Gabse/DMX2SGM/Documentation/20190912_201713.jpg

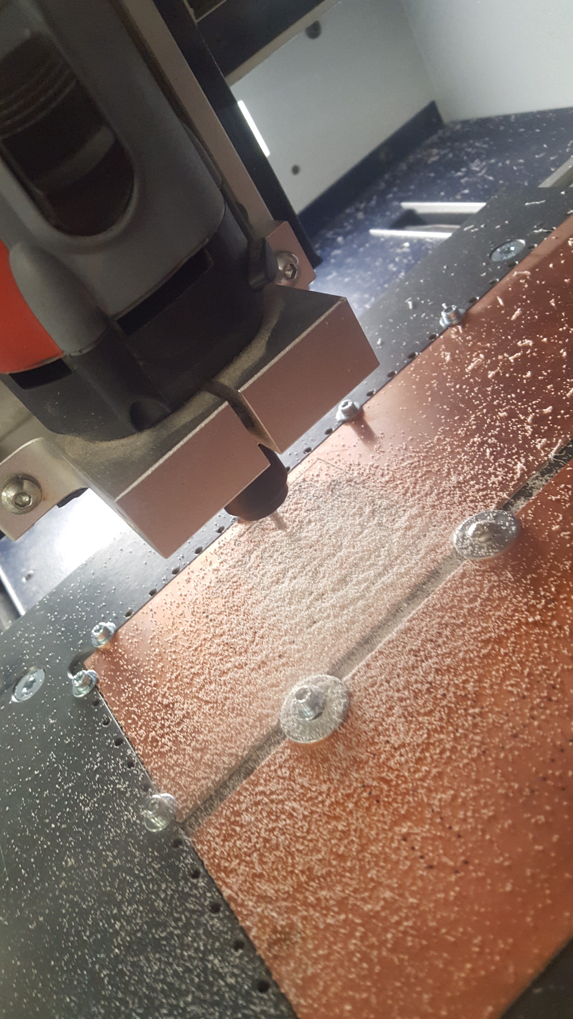
Documentation/20190912_201713.jpg
