Gabse/DMX2SGM/Documentation/20190912_203418.jpg

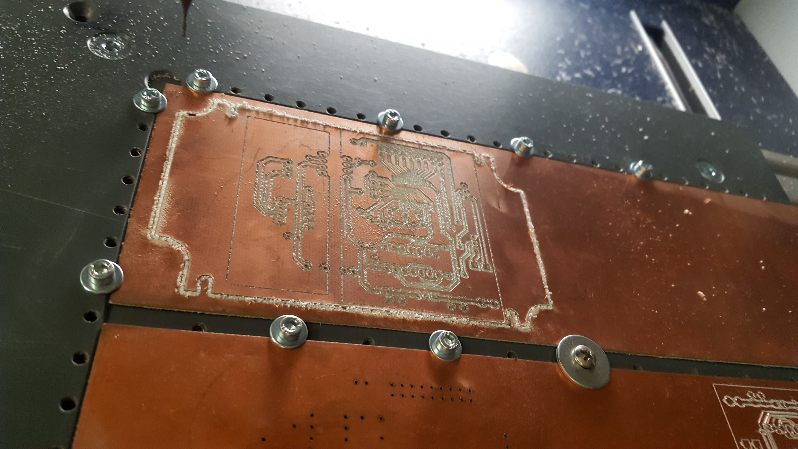
Documentation/20190912_203418.jpg
