Gabse/DMX2SGM/Documentation/20190913_112044.jpg

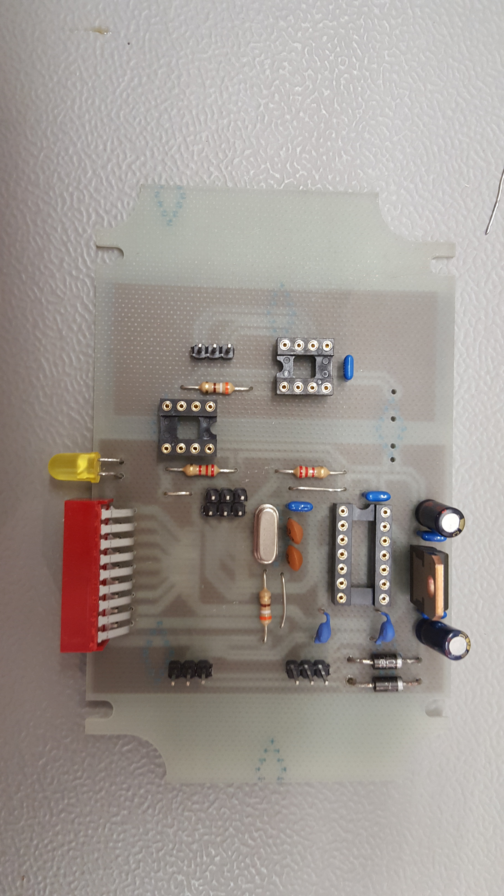
Documentation/20190913_112044.jpg
