Gabse/DMX2SGM/Documentation/20191015_202654.jpg

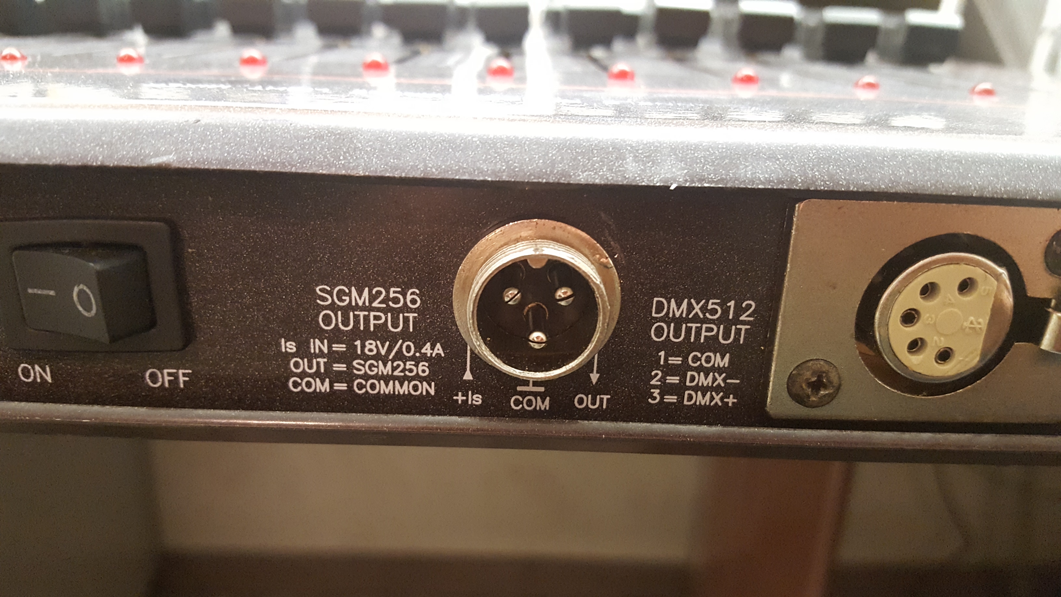
Documentation/20191015_202654.jpg
