Gabse/DMX2SGM/Documentation/20191113_215739.jpg

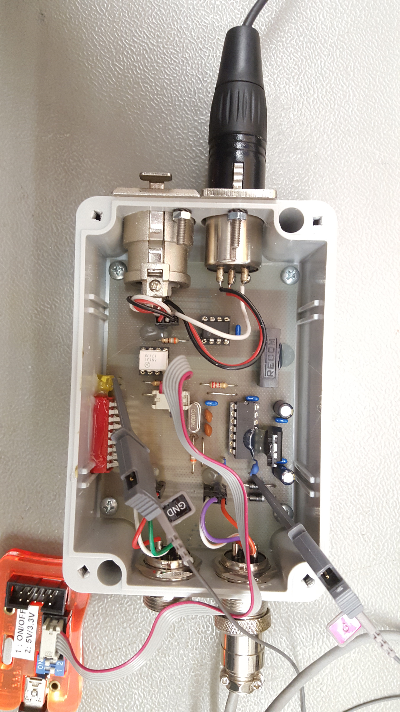
Documentation/20191113_215739.jpg
