Gabse/DMX2SGM/Documentation/20191113_215922.jpg

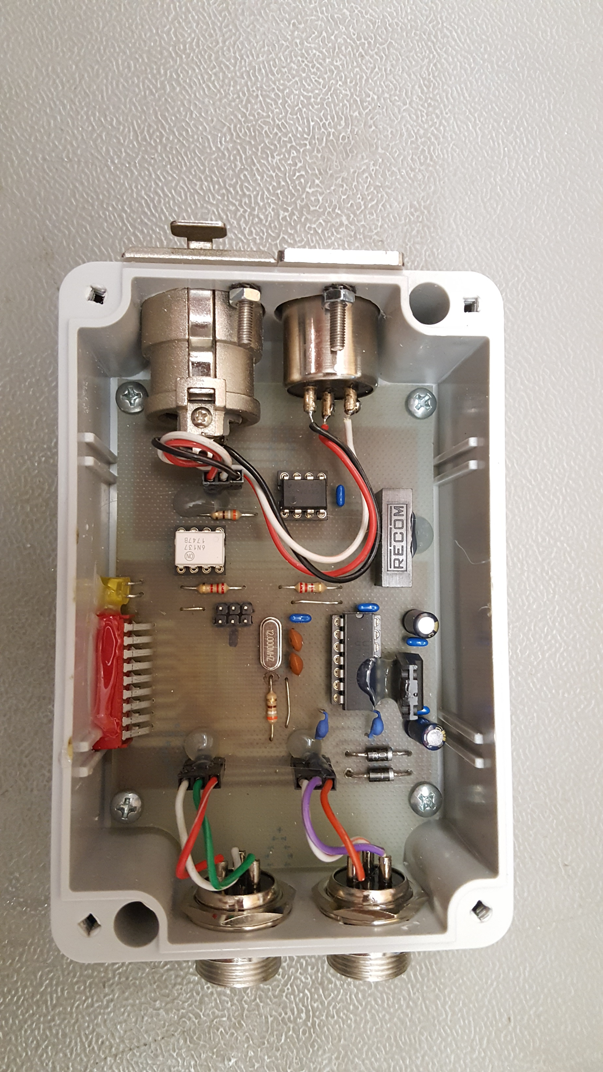
Documentation/20191113_215922.jpg
