Gabse/DMX2SGM/Documentation/20191124_184707.jpg

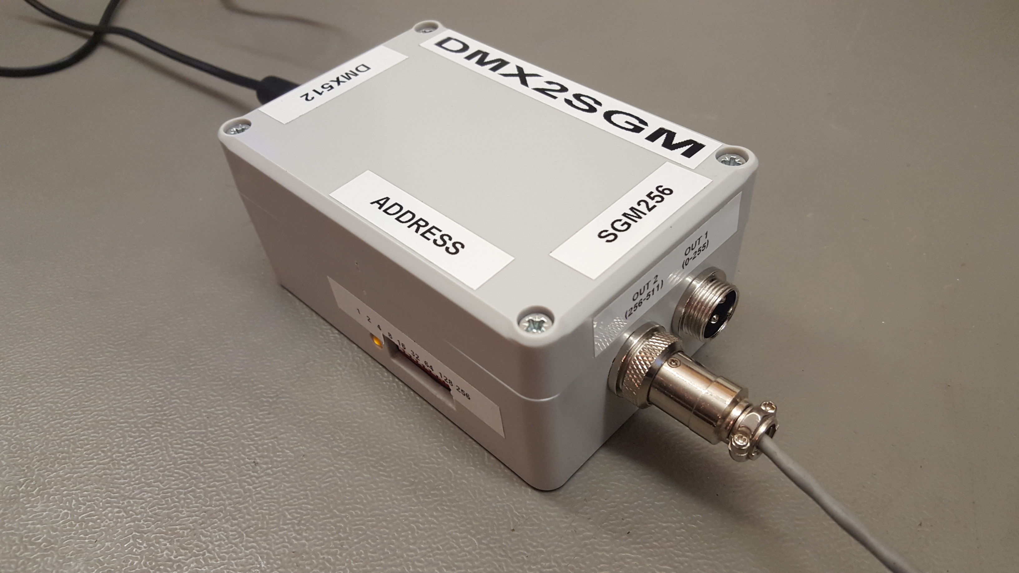
Documentation/20191124_184707.jpg
